danwerner21/Dragon64/images/display.jpg

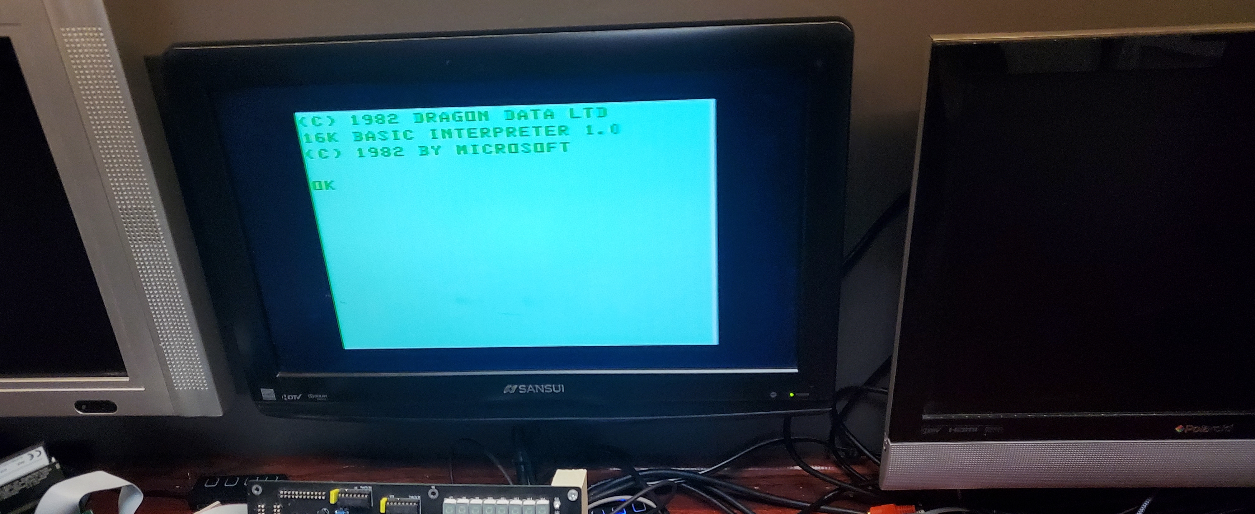
images/display.jpg
