danwerner21/Dragon64/images/pic3.jpg

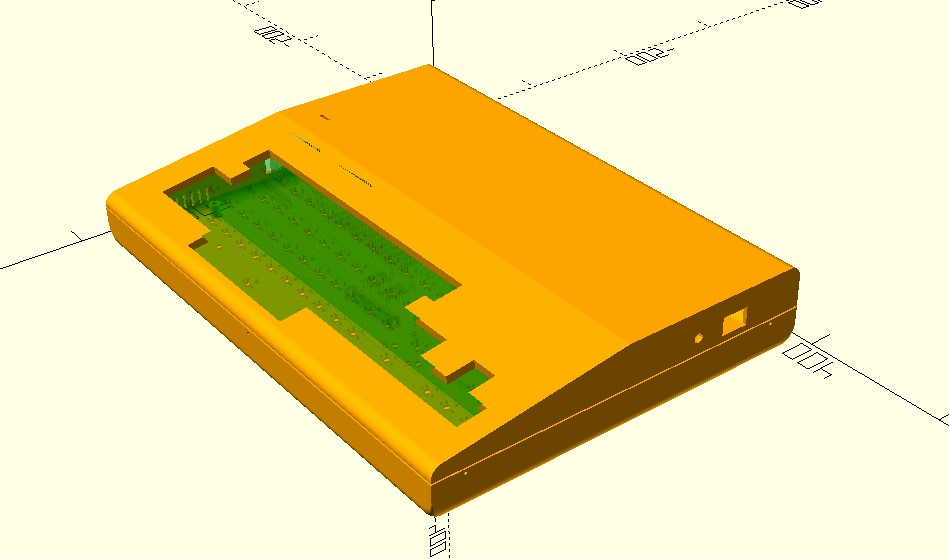
images/pic3.jpg
