danwerner21/Dragon64/images/pic4.jpg

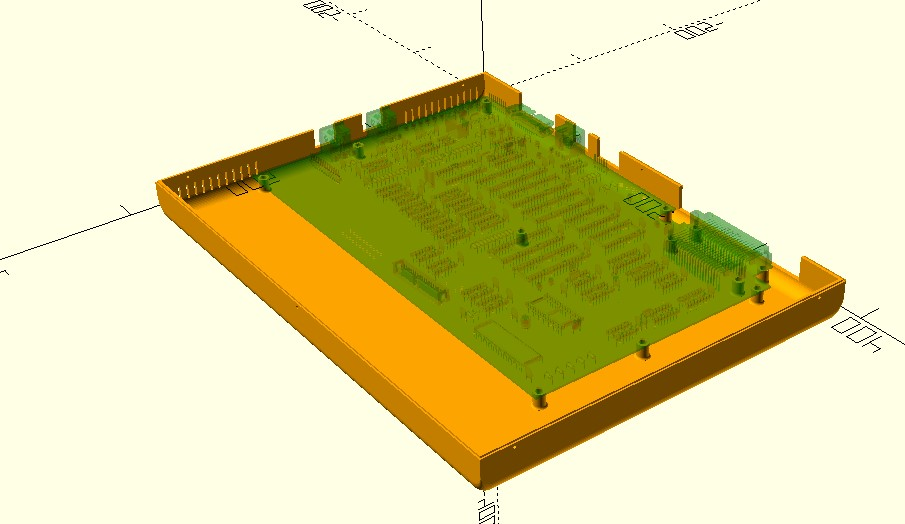
images/pic4.jpg
