danwerner21/Dragon64/images/system1.jpg

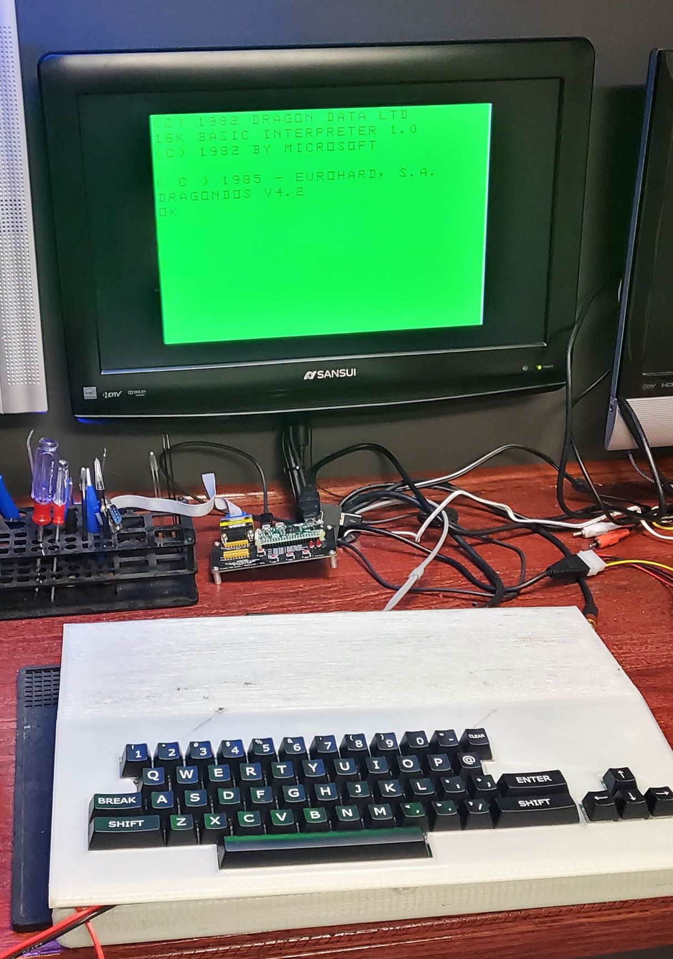
images/system1.jpg
